oprobst/Bogenampel/specs/005-ota-maintenance-mode/checklists/requirements.md

# Specification Quality Checklist: Receiver OTA Maintenance Mode (button-at-boot)

**Purpose**: Validate specification completeness and quality before proceeding to planning
**Created**: 2026-06-13
**Feature**: [spec.md](../spec.md)

## Content Quality

- [x] No implementation details (languages, frameworks, APIs)
- [x] Focused on user value and business needs
- [x] Written for non-technical stakeholders
- [x] All mandatory sections completed

## Requirement Completeness

- [x] No [NEEDS CLARIFICATION] markers remain
- [x] Requirements are testable and unambiguous
- [x] Success criteria are measurable
- [x] Success criteria are technology-agnostic (no implementation details)
- [x] All acceptance scenarios are defined
- [x] Edge cases are identified
- [x] Scope is clearly bounded
- [x] Dependencies and assumptions identified

## Feature Readiness

- [x] All functional requirements have clear acceptance criteria
- [x] User scenarios cover primary flows
- [x] Feature meets measurable outcomes defined in Success Criteria
- [x] No implementation details leak into specification

## Notes

- Items marked incomplete require spec updates before `/speckit.clarify` or `/speckit.plan`.
- Validation result (2026-06-13): all items pass.
  - "ESP-NOW", "WiFi", "access point", "indicator LED", "button" are treated as user-facing
    product/hardware terms (the receiver's existing physical controls and its radio link), not
    implementation choices — kept because removing them would make the requirements untestable for
    this embedded device.
  - Zero [NEEDS CLARIFICATION] markers: the one open design decision (how OTA and the radio link
    coexist) was resolved with the user before writing the spec (on-demand maintenance mode).
