oprobst/Bogenampel/specs/004-v3-esp32-port/checklists/requirements.md

# Specification Quality Checklist: Bogenampel V3 Hardware Port (ESP32 + e-Paper + ESP-NOW)

**Purpose**: Validate specification completeness and quality before proceeding to planning
**Created**: 2026-06-09
**Feature**: [spec.md](../spec.md)

## Content Quality

- [x] No implementation details (languages, frameworks, APIs) — *see note below*
- [x] Focused on user value and business needs
- [x] Written for non-technical stakeholders
- [x] All mandatory sections completed

## Requirement Completeness

- [x] No [NEEDS CLARIFICATION] markers remain
- [x] Requirements are testable and unambiguous
- [x] Success criteria are measurable
- [x] Success criteria are technology-agnostic (no implementation details) — *see note below*
- [x] All acceptance scenarios are defined
- [x] Edge cases are identified
- [x] Scope is clearly bounded
- [x] Dependencies and assumptions identified

## Feature Readiness

- [x] All functional requirements have clear acceptance criteria
- [x] User scenarios cover primary flows
- [x] Feature meets measurable outcomes defined in Success Criteria
- [x] No implementation details leak into specification — *see note below*

## Notes

- **Deliberate exception on "no implementation details"**: this feature IS a hardware port — the
  target MCUs, the display technology, the radio transport and the pin assignments are the
  requirement, not an implementation choice. They are fixed by the finalized V3 schematics in
  `Schaltung_v3/` and were confirmed by the user (including the decision to rework the brightness
  poti to pin D1 and to keep the V2 two-button menu concept). The spec confines these facts to
  the "Hardware Constraints" section and the platform comparison table; behavioral requirements
  (FR-001…FR-010, FR-012…FR-019 in their observable effects) remain implementation-free. Software
  implementation choices (libraries, ESP-NOW frame format, task structure) are left to the
  planning phase.
- All user decisions captured: two-button navigation with wrap-around (as lived in V2),
  brightness poti reworked from D5 to D1, spec-kit workflow, V2 code untouched.
- Ready for `/speckit.plan` (or `/speckit.clarify` if desired).
