oprobst/Bogenampel/specs/001-archery-timer/checklists/requirements.md

# Specification Quality Checklist: Wireless Archery Range Timer System

**Purpose**: Validate specification completeness and quality before proceeding to planning
**Created**: 2025-12-04
**Feature**: [spec.md](../spec.md)

## Content Quality

- [x] No implementation details (languages, frameworks, APIs)
- [x] Focused on user value and business needs
- [x] Written for non-technical stakeholders
- [x] All mandatory sections completed

## Requirement Completeness

- [x] No [NEEDS CLARIFICATION] markers remain
- [x] Requirements are testable and unambiguous
- [x] Success criteria are measurable
- [x] Success criteria are technology-agnostic (no implementation details)
- [x] All acceptance scenarios are defined
- [x] Edge cases are identified
- [x] Scope is clearly bounded
- [x] Dependencies and assumptions identified

## Feature Readiness

- [x] All functional requirements have clear acceptance criteria
- [x] User scenarios cover primary flows
- [x] Feature meets measurable outcomes defined in Success Criteria
- [x] No implementation details leak into specification

## Validation Results

**Status**: PASSED

All checklist items have been validated and passed. The specification is ready for the next phase.

### Detailed Validation Notes:

1. **Content Quality**: The specification focuses on what the system does (timer control, visual display, audio feedback) and why (range safety, shooter coordination) without mentioning specific technologies like Arduino, nRF24L01+, or WS2812B LEDs.

2. **Requirement Completeness**: All 18 functional requirements are testable and unambiguous. No clarification markers exist. Requirements clearly define system behavior without implementation details.

3. **Success Criteria**: All 10 success criteria are measurable and technology-agnostic:
   - Distance-based metrics (20+ meters)
   - Time-based metrics (±1 second precision, <500ms transitions, <5 second initialization)
   - Reliability metrics (<1% failure rate, 8+ hour operation)
   - Usability metrics (95% success rate without documentation)

4. **User Scenarios**: Five prioritized user stories (P1-P5) cover the complete feature scope from core functionality to maintenance. Each story is independently testable with clear acceptance scenarios using Given-When-Then format.

5. **Edge Cases**: Six edge cases identified covering signal interruption, rapid input, mode changes during operation, initial state, range limits, and power issues.

## Next Steps

The specification is ready for:
- `/speckit.plan` - Proceed directly to implementation planning
- OR `/speckit.clarify` - Optional clarification if additional questions arise

No blocking issues found. Feature is well-specified and ready for planning phase.
