oprobst/Bogenampel/specs/006-shutdown-alarm-gesten/checklists/requirements.md

# Specification Quality Checklist: Entkopplung von Ausschalten und Alarm

**Purpose**: Validate specification completeness and quality before proceeding to planning
**Created**: 2026-08-02
**Feature**: [spec.md](../spec.md)

## Content Quality

- [x] No implementation details (languages, frameworks, APIs)
- [x] Focused on user value and business needs
- [x] Written for non-technical stakeholders
- [x] All mandatory sections completed

## Requirement Completeness

- [x] No [NEEDS CLARIFICATION] markers remain
- [x] Requirements are testable and unambiguous
- [x] Success criteria are measurable
- [x] Success criteria are technology-agnostic (no implementation details)
- [x] All acceptance scenarios are defined
- [x] Edge cases are identified
- [x] Scope is clearly bounded
- [x] Dependencies and assumptions identified

## Feature Readiness

- [x] All functional requirements have clear acceptance criteria
- [x] User scenarios cover primary flows
- [x] Feature meets measurable outcomes defined in Success Criteria
- [x] No implementation details leak into specification

## Notes

- **Alle Punkte erfüllt (Stand 2026-08-02, 2. Durchlauf).**
- Die drei ursprünglich offenen Marker (FR-007, FR-009, FR-010) wurden am
  2026-08-02 vom Auftraggeber entschieden: Dreifachklick mit max. 400 ms
  Klickabstand, beide Tasten gleichwertig, gültig nur in „Schießbetrieb" und
  „Pfeile holen".
- Items marked incomplete require spec updates before `/speckit.clarify` or `/speckit.plan`
