oprobst/Bogenampel/specs/001-benutzer-fuehrung/checklists/requirements.md

# Specification Quality Checklist: Archery Tournament Control System - User Guidance

**Purpose**: Validate specification completeness and quality before proceeding to planning
**Created**: 2025-12-13
**Feature**: [spec.md](../spec.md)

## Content Quality

- [x] No implementation details (languages, frameworks, APIs)
- [x] Focused on user value and business needs
- [x] Written for non-technical stakeholders
- [x] All mandatory sections completed

## Requirement Completeness

- [x] No [NEEDS CLARIFICATION] markers remain
- [x] Requirements are testable and unambiguous
- [x] Success criteria are measurable
- [x] Success criteria are technology-agnostic (no implementation details)
- [x] All acceptance scenarios are defined
- [x] Edge cases are identified
- [x] Scope is clearly bounded
- [x] Dependencies and assumptions identified

## Feature Readiness

- [x] All functional requirements have clear acceptance criteria
- [x] User scenarios cover primary flows
- [x] Feature meets measurable outcomes defined in Success Criteria
- [x] No implementation details leak into specification

## Notes

### Clarifications Resolved (2025-12-13)

All 3 clarification questions have been resolved with user input:

1. **FR-003** - Splash screen duration: **3 seconds** (User selected Option B)
2. **User Story 4, Scenario 3** - Configuration reset behavior: **Retain previous settings** (User selected Option B)
3. **User Story 5, Scenario 3** - Post-alarm display behavior: **Return immediately to previous state without confirmation** (User selected Option C)

### Status

**VALIDATION COMPLETE** - All checklist items pass. Specification is ready for planning phase.

Next step: Run `/speckit.plan` to create the implementation plan.
