oprobst/Bogenampel/specs/003-startup-logo-splash/checklists/requirements.md

# Specification Quality Checklist: Startup-Logo und Splash Screen

**Purpose**: Validate specification completeness and quality before proceeding to planning
**Created**: 2025-12-13
**Feature**: [spec.md](../spec.md)

## Content Quality

- [x] No implementation details (languages, frameworks, APIs)
- [x] Focused on user value and business needs
- [x] Written for non-technical stakeholders
- [x] All mandatory sections completed

## Requirement Completeness

- [x] No [NEEDS CLARIFICATION] markers remain
- [x] Requirements are testable and unambiguous
- [x] Success criteria are measurable
- [x] Success criteria are technology-agnostic (no implementation details)
- [x] All acceptance scenarios are defined
- [x] Edge cases are identified
- [x] Scope is clearly bounded
- [x] Dependencies and assumptions identified

## Feature Readiness

- [x] All functional requirements have clear acceptance criteria
- [x] User scenarios cover primary flows
- [x] Feature meets measurable outcomes defined in Success Criteria
- [x] No implementation details leak into specification

## Validation Summary

**Status**: ✓ PASSED - All quality criteria met
**Validation Date**: 2025-12-13
**Clarifications Resolved**: 1 (button press behavior during splash screen)

### Changes Made During Validation
1. Resolved [NEEDS CLARIFICATION] for button press: Any key press skips to main mode
2. Added FR-007: System must end splash screen on any key press
3. Added acceptance scenario 3 in User Story 2: Key press behavior
4. Added SC-006: Key press response time requirement

## Notes

- All validation items passed
- Specification is ready for `/speckit.clarify` or `/speckit.plan`
