oprobst/Bogenampel/Empfaenger/Config.h

/**
 * @file Config.h
 * @brief Zentrale Konfigurationsdatei für Bogenampel V3 Empfänger (Anzeigeeinheit)
 *
 * Enthält alle Hardware-Pin-Definitionen, Timing-Konstanten und
 * Konfigurationsparameter für den Empfänger.
 *
 * Hardware: Seeed XIAO ESP32C3 (U3) auf der PD-12V-Platine (Rev. 2026-08-03)
 * - WS2811 LED Strip (12V, IC-gesteuert, RGB; 7-Segment + Gruppen), direkt am 12V-Netz
 * - ESP-NOW Funk (integriert, kein externes Modul)
 * - Piezo-Transducer 12V über BC337 (Q3), Lüfter über BSS138 (Q2, Low-Side-PWM)
 * - 3 Potis (Lautstärke, Helligkeit, Lüfter-Drehzahl), Debug-Taster, Status-LED
 *
 * Versorgung (PD-12V-Platine, löst den USB-5V-Aufbau mit Step-up ab):
 * - USB-C → CH224K (U2) verhandelt 12 V → Verpolungsschutz Q1 (AO3401A) + TVS D2
 *   → +12V-Netz: LED-Strip (J7), Piezo (J8), Lüfter (J6)
 * - TSR0.5-2433 (U4): 12 V → 3V3, speist den XIAO über den 3V3-Pin (VUSB unbeschaltet)
 * - L7805 (U1): 12 V → 5 V, versorgt ausschließlich den Pegelwandler U5
 * - U5 74AHCT1G125: Pegelwandler 3,3 → 5 V in der LED-Datenleitung (/OE fest an GND,
 *   nicht invertierend), Ausgang über R14 330 Ω an J7 Pin 2 — ersetzt den früheren
 *   direkten 3,3-V-Anschluss, der Farbkipper (Gelb/Weiß) verursacht hat
 *
 * Verbindliche Pin-Quelle: specs/004-v3-esp32-port/contracts/hardware-pins.md
 * (extrahiert aus Schaltung-Empfaenger/Empfaenger.kicad_sch)
 *
 * ESP32-C3-Strapping-Hinweise (alle im Schaltplan gelöst, Stand 2026-06-10):
 * - GPIO2/D0 (Lautstärke-Poti): Fußpunkt an D4 (POTI_GND) statt GND
 * - GPIO9/D9 (Status-LED): aktiv LOW (3V3 → LED → R6 → Pin)
 * - GPIO8/D8: frei (Lüfter-Tacho bewusst nicht angeschlossen)
 *
 * @date 2026-06-11
 * @version 3.0
 */

#pragma once

#include <Arduino.h>

//=============================================================================
// DEBUG-KONFIGURATION (muss VOR allen anderen Definitionen stehen!)
//=============================================================================

// Debugging aktivieren/deaktivieren
#define DEBUG_ENABLED 0  // 1 = Debug-Ausgaben an, 0 = aus

// Verkürzte Zeiten für Testläufe. Default 0 — eingeschaltet wird das NICHT hier,
// sondern über -DDEBUG_SHORT_TIMES=1 aus der platformio.ini (env:empfaenger-debug
// / empfaenger-debug-ota). So kann ein Testbuild mit 6-Sekunden-Passe nicht
// versehentlich im Feld landen, und Sender und Empfänger werden immer bewusst
// als Paar umgestellt (die Zeittabelle muss auf beiden Geräten gleich sein).
#ifndef DEBUG_SHORT_TIMES
#define DEBUG_SHORT_TIMES 0  // 1 = Verkürzte Zeiten, 0 = Normale Zeiten
#endif

//=============================================================================
// HARDWARE PIN-DEFINITIONEN (XIAO-Nummerierung → GPIO)
//=============================================================================

namespace Pins {

    //-------------------------------------------------------------------------
    // Analoge Eingänge: Potis (alle ADC1 — ADC2 ist mit aktivem Funk unbrauchbar!)
    //-------------------------------------------------------------------------
    constexpr uint8_t VOLUME_POTI     = 2;  // D0/GPIO2 (ADC1_CH2): Lautstärke (J3),
                                            // Schleifer über R3 1k; Fußpunkt an POTI_GND!
    constexpr uint8_t BRIGHTNESS_POTI = 3;  // D1/GPIO3 (ADC1_CH3): Helligkeit (J4),
                                            // über R4 1k (umverdrahtet von D5 — GPIO7 hat keinen ADC)
    constexpr uint8_t FAN_POTI        = 4;  // D2/GPIO4 (ADC1_CH4): Lüfter-Drehzahl (J2),
                                            // Schleifer über R5 1k

    //-------------------------------------------------------------------------
    // Geschalteter Poti-Fußpunkt (Strapping-Fix GPIO2, Befund 2)
    //-------------------------------------------------------------------------
    constexpr uint8_t POTI_GND = 6;  // D4/GPIO6: Fußpunkt des Lautstärke-Potis (J3 Pin 3);
                                     // beim Reset hochohmig → GPIO2 liegt HIGH (Boot ok);
                                     // in setup() FRÜH auf OUTPUT + LOW setzen!

    //-------------------------------------------------------------------------
    // Ausgänge: Signalgeber und Lüfter
    //-------------------------------------------------------------------------
    constexpr uint8_t BUZZER  = 5;   // D3/GPIO5 (LEDC): Piezo 12V-Transducer (J8) über
                                     // R10 2k2 → BC337 (Q3), R12 10k Basis-Pulldown;
                                     // R15 2k2 vom Collector nach +12V (Entlade-Pfad —
                                     // ohne den schwingt der Piezo nicht, nur Brummen).
                                     // ACHTUNG: auf der PD-Platine 2k2 statt der früheren
                                     // 470 Ω (5,4 statt 25 mA) — dafür jetzt 12 V statt 5 V
                                     // am Piezo. Falls zu leise: R15 verkleinern (0,5-W-Typ).
                                     // (GPIO5 ist ADC2, wird aber rein digital genutzt)
    constexpr uint8_t FAN_PWM = 21;  // D6/GPIO21 (LEDC): Gate des BSS138 (Q2, J6 Pin 4);
                                     // Q2 invertiert (Open-Drain auf der PWM-Leitung):
                                     // Gate HIGH = Leitung LOW = langsam! R11 10k =
                                     // Pull-up an 3V3 am Gate → PWM-Leitung beim Boot LOW,
                                     // Lüfter auf Minimaldrehzahl, bis die Firmware
                                     // übernimmt (früh Duty setzen!). R13 10k zieht die
                                     // PWM-Leitung bei sperrendem Q2 sauber auf 3V3.

    //-------------------------------------------------------------------------
    // Ausgänge: LEDs
    //-------------------------------------------------------------------------
    constexpr uint8_t LED_STRIP  = 10;  // D10/GPIO10: WS2811 Data → U5 (74AHCT1G125,
                                        // 3,3→5 V) → R14 330Ω → J7 Pin 2.
                                        // U5 hat KEINEN Eingangs-Pulldown: den Pin in
                                        // setup() SOFORT auf OUTPUT LOW legen, sonst
                                        // floatet der Buffer-Eingang bis FastLED.addLeds()
                                        // und schiebt Müll auf die Datenleitung.
    constexpr uint8_t STATUS_LED = 9;   // D9/GPIO9: Status-LED D3 — AKTIV LOW!
                                        // (3V3 → LED → R9 220Ω → Pin sinkt Strom;
                                        // Strapping-Fix Befund 3, Firmware invertiert)

    //-------------------------------------------------------------------------
    // Eingänge: Taster
    //-------------------------------------------------------------------------
    constexpr uint8_t BTN_DEBUG = 20;  // D7/GPIO20 (J5): Debug-/Testtaster gegen GND,
                                       // INPUT_PULLUP, aktiv LOW

    // Frei/Reserve: D5/GPIO7, D8/GPIO8 (Tacho bewusst nicht angeschlossen)

} // namespace Pins

// Status-LED-Polarität (aktiv LOW, siehe oben)
constexpr uint8_t STATUS_LED_ON  = LOW;
constexpr uint8_t STATUS_LED_OFF = HIGH;

//=============================================================================
// OTA (WiFi-Station + ArduinoOTA, nur im OTA-Wartungsmodus)
//=============================================================================

// wifi_credentials.h (gitignored) definiert WIFI_SSID_OVERRIDE + WIFI_PASS_OVERRIDE.
// Vorlage: wifi_credentials.h.example im Repo-Root.
#if __has_include("wifi_credentials.h")
    #include "wifi_credentials.h"
#endif

namespace OTA {

    constexpr const char* HOSTNAME = "bogenampel-empfaenger";
    // OTA-Passwort (WPA2, min. 8 Zeichen) — ArduinoOTA-Auth (FR-012)
    constexpr const char* PASSWORD = "bogenampel";

    // Heimnetz-WLAN für den OTA-Wartungsmodus — aus wifi_credentials.h. Ohne
    // Zugangsdaten bleibt das Gerät im Wartungsmodus im CONNECTING-Blinken
    // (kein SoftAP-Fallback mehr, FR-009). ESP-NOW läuft im Wartungsmodus nicht.
#ifdef WIFI_SSID_OVERRIDE
    constexpr const char* WIFI_SSID = WIFI_SSID_OVERRIDE;
    constexpr const char* WIFI_PASS = WIFI_PASS_OVERRIDE;
#else
    constexpr const char* WIFI_SSID = "";
    constexpr const char* WIFI_PASS = "";
#endif
    constexpr uint16_t WIFI_TIMEOUT = 10000;  // ms bis zum erneuten WiFi-Connect-Versuch (OTA-Wartungsmodus)

} // namespace OTA

//=============================================================================
// OTA-WARTUNGSMODUS — Status-LED-Signalmuster (D9, aktiv LOW)
// Drei unterscheidbare Muster, alle Zeiten sind Zielwerte (±~50 ms Toleranz):
//   CONNECTING (FR-004a): schnelles kurzes Blitzen      (100 ms an / 500 ms aus)
//   READY      (FR-004b): langsames gleichmäßiges Blinken (500 ms an / 500 ms aus)
//   UPDATING   (FR-004c): leuchtet, alle 500 ms kurz aus  (500 ms an / 100 ms aus)
//=============================================================================

namespace OtaSignal {

    constexpr uint16_t CONNECTING_PERIOD_MS = 600;   // FR-004a
    constexpr uint16_t CONNECTING_ON_MS     = 100;
    constexpr uint16_t READY_PERIOD_MS      = 1000;  // FR-004b
    constexpr uint16_t READY_ON_MS          = 500;
    constexpr uint16_t UPDATING_PERIOD_MS   = 600;   // FR-004c
    constexpr uint16_t UPDATING_ON_MS       = 500;

} // namespace OtaSignal

//=============================================================================
// FUNK (ESP-NOW)
//=============================================================================

namespace Radio {

    // WLAN-Kanal (fest, beide Geräte identisch — espnow-protocol.md)
    constexpr uint8_t CHANNEL = 1;

} // namespace Radio

//=============================================================================
// TIMING-KONSTANTEN
//=============================================================================

namespace Timing {

    // Status-LED-Feedback
    constexpr uint16_t LED_BLINK_DURATION_MS = 100;  // Kurzes Blinken bei Empfang

    // Button Debouncing
    constexpr uint8_t DEBOUNCE_MS = 50;  // 50ms Entprellzeit

    // Buzzer-Feedback
    // Resonanzfrequenz des Transducers (Datenblatt CPS-4013-110PM, rated 3250 Hz):
    // ein Piezo ist GENAU bei seiner Resonanz am lautesten — daneben (vorher 2700 Hz)
    // kaum hörbar. Das ist der Lautstärke-Hebel.
    constexpr uint16_t BUZZER_FREQUENCY_HZ = 3250;

    // Poti-Abtastung (alle Regler live, ≥ 10 Hz — FR-021/FR-022/FR-023)
    constexpr uint16_t POTI_UPDATE_INTERVAL_MS = 100;  // 10 Hz

    // Regler-Vorschau: beim Drehen an Lautstärke-/Helligkeits-Poti läuft eine
    // Vorschau (Ton bzw. "888"-Anzeige), die noch bis zu dieser Zeit nach der
    // letzten Bewegung nachklingt.
    constexpr uint16_t PREVIEW_HOLD_MS = 1000;  // max. 1 s Nachlauf

    // Schießbetrieb — Vorbereitungsphase (Wert wie Sender/Config.h)
    #if DEBUG_SHORT_TIMES
        constexpr uint16_t PREPARATION_TIME_MS = 5000;   // 5 Sekunden (DEBUG)
    #else
        constexpr uint16_t PREPARATION_TIME_MS = 10000;  // 10 Sekunden Vorbereitungsphase
    #endif

    //-------------------------------------------------------------------------
    // Verkürzte Schießzeit für Testläufe (DEBUG_SHORT_TIMES)
    //-------------------------------------------------------------------------
    // 120 s → 6 s, 240 s → 12 s (zusammen mit der 5-s-Vorbereitung läuft eine
    // komplette Passe damit in unter einer Minute durch statt in Minuten).
    //
    // ACHTUNG: Diese Abbildung MUSS in Sender/Config.h und Empfaenger/Config.h
    // identisch bleiben. Der Empfänger zählt die Passe AUTONOM (FR-004) und
    // bekommt per Funk nur CMD_START_120/CMD_START_240 — nie die Dauer selbst.
    // Weichen die beiden Tabellen ab, laufen Ampel und Anzeige auseinander und
    // das Passenende fällt auf zwei verschiedene Sekunden.
    constexpr uint16_t SHOOT_DEBUG_120_SEC = 6;
    constexpr uint16_t SHOOT_DEBUG_240_SEC = 12;

    /**
     * @brief Nominale Schießzeit (120/240 s) → tatsächliche Countdown-Dauer
     * @param nominalSeconds Schießzeit aus dem START-Kommando (120 oder 240)
     * @return im Normalbetrieb der Wert selbst, mit DEBUG_SHORT_TIMES die
     *         verkürzte Testdauer
     */
    constexpr uint16_t shootingSeconds(uint16_t nominalSeconds) {
    #if DEBUG_SHORT_TIMES
        return (nominalSeconds >= 240) ? SHOOT_DEBUG_240_SEC : SHOOT_DEBUG_120_SEC;
    #else
        return nominalSeconds;
    #endif
    }

    // Orange-Phase am Ende der Schießzeit. Im Debug-Modus NICHT 5 s: bei einer
    // 6-s-Passe wäre damit fast der ganze Countdown orange und die Phase als
    // Signal wertlos. 2 s halten den Anteil (33 % / 17 %) nah am Normalbetrieb
    // (30 s von 120 s = 25 %).
    #if DEBUG_SHORT_TIMES
        constexpr uint32_t ORANGE_THRESHOLD_SEC = 2;   // DEBUG
    #else
        constexpr uint32_t ORANGE_THRESHOLD_SEC = 30;  // letzte 30 Sekunden
    #endif

} // namespace Timing

//=============================================================================
// ADC-HILFSFUNKTIONEN
//=============================================================================

namespace Adc {

    // Leichte softwareseitige Rauschunterdrückung: Mehrfachmessung mitteln
    // (Oversampling). Reduziert weißes ADC-Rauschen ~√N, ohne Latenz über die
    // Zeit (Reglerstellung bleibt sofort sichtbar). Default 6 Samples.
    inline uint16_t readAveraged(uint8_t pin, uint8_t samples = 6) {
        uint32_t sum = 0;
        for (uint8_t i = 0; i < samples; i++) {
            sum += analogRead(pin);
        }
        return (uint16_t)(sum / samples);
    }

} // namespace Adc

//=============================================================================
// POTI-ORIENTIERUNG (eine Stelle für alle drei Regler)
//=============================================================================

namespace Poti {

    // ESP32-C3-ADC ist 12-bit.
    constexpr uint16_t ADC_MAX = 4095;

    // Drehrichtung der Regler, HARDWARE-ABHÄNGIG — hier und NUR hier umstellen:
    //   true  = Aufdrehen liefert den HÖHEREN ADC-Wert (PD-12V-Platine,
    //           Rev. 2026-08-03: Schleifer zwischen GND und 3V3 regulär verdrahtet)
    //   false = Poti verpolt verbaut (Vorserien-Aufbau bis 2026-08-05) — dort
    //           lieferte Aufdrehen den KLEINEREN Wert und die Firmware invertierte
    //           an fünf Stellen einzeln.
    // Befund 2026-10-01 auf der fertigen Platine: alle drei Regler liefen falsch
    // herum (aufdrehen = dunkler/leiser/langsamer), weil die Software noch
    // invertierte. Verdrahtung bleibt, Invertierung ist hiermit abgeschaltet.
    constexpr bool ASCENDING = true;

    /**
     * @brief Rohwert → Reglerstellung, unabhängig von der Verdrahtung
     * @param raw gemittelter ADC-Rohwert (0…ADC_MAX)
     * @return 0 = Regler am unteren Anschlag (aus/dunkel/langsam),
     *         ADC_MAX = oberer Anschlag (laut/hell/schnell)
     *
     * Alle Kennlinien und Schwellen im Projekt rechnen mit DIESEM Wert, nie mit
     * dem Rohwert — damit beschreibt ASCENDING die Hardware an genau einer Stelle.
     */
    inline uint16_t level(uint16_t raw) {
        uint16_t clamped = (raw > ADC_MAX) ? ADC_MAX : raw;
        return ASCENDING ? clamped : (uint16_t)(ADC_MAX - clamped);
    }

} // namespace Poti

//=============================================================================
// LAUTSTÄRKE-POTI (D0)
//=============================================================================

namespace Volume {

    // Unterhalb dieser Reglerstellung (Poti::level, NICHT Rohwert) ist der Buzzer
    // KOMPLETT STUMM; darüber quadratische Kennlinie bis volle Lautstärke am
    // oberen Anschlag. Bewusst sehr schmal (2026-10-01): stumm wird es nur noch
    // direkt am unteren Anschlag, der nutzbare Lautstärkeweg beginnt sofort
    // danach. Falls das Stummschalten am Anschlag nicht greift, liegt der
    // ADC-Nullpunkt des Exemplars über diesem Wert → Schwelle wieder anheben.
    constexpr uint16_t OFF_THRESHOLD = 5;  // nur der unterste Anschlag ist stumm

} // namespace Volume

//=============================================================================
// LED STRIP KONFIGURATION (WS2811 12V, IC-gesteuert, RGB)
//=============================================================================

namespace LEDStrip {

    // LED Strip Konfiguration (WS2811 12V — 1 Pixel pro schneidbarem Abschnitt):
    // Strip-Reihenfolge (vom HW-Aufbau bestätigt 2026-06-17):
    // - Gruppe C/D: 12 Pixel (LED 1-12,  Array Index 0-11)
    // - Gruppe A/B: 12 Pixel (LED 13-24, Array Index 12-23)
    // - 3 Digits × 7 Segmente × 2 Pixel = 42 Pixel (Array Index 24-65)
    // Total: 66 Pixel

    // Montage-Orientierung (2026-08-06, fertig verdrahtete Tafel): Der Strip-Anfang
    // (Data-In) sitzt in Leserichtung am FALSCHEN Ende — ohne Korrektur steht die
    // komplette Anzeige exakt um 180° auf dem Kopf. Die Verlegung ist in beiden
    // Bereichen punktsymmetrisch, die Drehung ist deshalb eine reine Indexumkehr
    // je Bereich:
    //   - Ziffernblock  (Index 24-65): 100er ↔ 1er tauschen UND je Ziffer die
    //     Segmente spiegeln (A↔D, B↔E, C↔F; G liegt auf der Drehachse) — das
    //     erledigt die umgekehrte Segment-Iteration in DisplayManager::displayDigit()
    // Die GRUPPENBALKEN sind davon ausdrücklich NICHT betroffen (am Aufbau geprüft
    // 2026-08-06): sie liegen nebeneinander an derselben Seite, nicht einander
    // gegenüber — die Drehung tauscht sie also nicht, ein Software-Tausch würde die
    // Zuordnung erst kaputt machen.
    // Auf false setzen, wenn die Tafel je andersherum aufgebaut/verdrahtet wird.
    constexpr bool ROTATE_180 = true;

    constexpr uint8_t GROUP_CD_LEDS = 12;      // LED 1-12  (Index 0-11)
    constexpr uint8_t GROUP_AB_LEDS = 12;      // LED 13-24 (Index 12-23)
    constexpr uint8_t GROUP_CD_START = 0;                            // C/D zuerst im Strip
    constexpr uint8_t GROUP_AB_START = GROUP_CD_START + GROUP_CD_LEDS;  // A/B direkt dahinter

    constexpr uint8_t LEDS_PER_SEGMENT = 2;    // 2 Pixel pro 7-Segment-Balken (12V-Streifen)
    constexpr uint8_t SEGMENTS_PER_DIGIT = 7;  // 7 Segmente pro Ziffer (B, A, F, G, C, D, E)
    constexpr uint8_t NUM_DIGITS = 3;          // 3 Ziffern (1er, 10er, 100er)
    constexpr uint8_t DIGIT_START = GROUP_CD_LEDS + GROUP_AB_LEDS;  // Ziffern beginnen nach beiden Gruppen

    constexpr uint8_t LEDS_PER_DIGIT = LEDS_PER_SEGMENT * SEGMENTS_PER_DIGIT;  // 14 Pixel pro Ziffer
    constexpr uint8_t TOTAL_LEDS = GROUP_AB_LEDS + GROUP_CD_LEDS + (NUM_DIGITS * LEDS_PER_DIGIT);

    // Start-Indizes für die einzelnen Ziffern (relativ zu DIGIT_START).
    // Die Namen bezeichnen die STELLENWERTIGKEIT, die Reihenfolge im Strip dreht
    // sich mit ROTATE_180 um (die mittlere 10er-Stelle bleibt in beiden Fällen
    // in der Mitte).
    constexpr uint8_t DIGIT_1_START = ROTATE_180 ? DIGIT_START + (2 * LEDS_PER_DIGIT)
                                                 : DIGIT_START;
    constexpr uint8_t DIGIT_10_START = DIGIT_START + LEDS_PER_DIGIT;            // 10er-Stelle (mitte)
    constexpr uint8_t DIGIT_100_START = ROTATE_180 ? DIGIT_START
                                                   : DIGIT_START + (2 * LEDS_PER_DIGIT);

    // Helligkeitsbereich für Poti-Steuerung (FR-022)
    constexpr uint8_t BRIGHTNESS_MIN = 38;      // 15% Helligkeit (weiter herunterdimmbar)

    // Design-Wert 255 (100 %), gültig ab der PD-12V-Platine (Rev. 2026-08-03):
    // Der Strip hängt dort direkt am 12V-PD-Netz, der XIAO an einem eigenen
    // 3V3-Regler (TSR0.5-2433) — der Strip kann die Logikversorgung also nicht mehr
    // in die Knie zwingen. Der frühere Deckel 64 stammt vom USB-5V-Aufbau mit
    // 5V→12V-Step-up (dort brach die 5V-Schiene bei voller Helligkeit ein →
    // ESP-Hang/Reset; stabil war nur ~15 %).
    // Strombedarf bei 255: 66 Pixel × ~20 mA je Farbkanal ≈ 1,3 A einfarbig
    // (Timer/Alarm) bzw. ~4 A bei Weiß → PD-Netzteil mit 12 V / ≥ 2 A verwenden.
    //   → Wert ist der obere Poti-Anschlag; bei Instabilität senken (Richtung
    //     BRIGHTNESS_MIN). ACHTUNG: Am alten USB-Aufbau NICHT mit 255 betreiben!
    constexpr uint8_t BRIGHTNESS_MAX = 255;     // 100 % (PD-12V-Platine)

} // namespace LEDStrip

//=============================================================================
// LÜFTER (PWM über BSS138, Drehzahl vom Poti — FR-023)
//=============================================================================

namespace Fan {

    constexpr uint32_t PWM_FREQUENCY_HZ = 25000;  // ≥ 25 kHz (4-Draht-Lüfter-Spec,
                                                  // außerhalb des Hörbereichs)
    constexpr uint8_t PWM_RESOLUTION_BITS = 8;    // Duty 0-255

    // Unterhalb dieser Reglerstellung (Poti::level, NICHT Rohwert) ist der Lüfter
    // aus (bzw. auf Minimaldrehzahl bei 4-Draht-Lüftern, die per PWM nicht
    // vollständig stoppen). ~2,3 % des Drehwegs am unteren Anschlag.
    constexpr uint16_t OFF_THRESHOLD = 95;  // 4095 − 4000 (Totband wie vorher)

    // Kennlinie Poti → Drehzahl: Gamma < 1 (konkav) verschiebt die Drehzahl-
    // änderung nach "früher" im Drehweg und macht die GEFÜHLTE Änderung gleich-
    // mäßiger (Luftstrom/Lärm ~ Drehzahl^~2,5 → γ≈0,4 linearisiert die Wahrnehmung).
    // Kleiner = mehr Spreizung nach unten; 1,0 = linear. Tunbar.
    constexpr float CURVE_GAMMA = 0.4f;

} // namespace Fan

//=============================================================================
// GRUPPEN-DEFINITIONEN (für 3-4 Schützen Modus)
//=============================================================================

namespace Groups {

    // Gruppen-Typen
    enum class Type : uint8_t {
        GROUP_AB = 0,  // Gruppe A/B
        GROUP_CD = 1   // Gruppe C/D
    };

    // Positions-Marker für 4-State Cycle
    enum class Position : uint8_t {
        POS_1 = 1,  // Position 1 (erste Hälfte der Passe)
        POS_2 = 2   // Position 2 (zweite Hälfte der Passe)
    };

} // namespace Groups

//=============================================================================
// SYSTEMKONSTANTEN
//=============================================================================

namespace System {

    // Versionsinformation
    constexpr const char* VERSION = "Bogenampel Empfaenger V3.0";
    constexpr const char* BUILD_DATE = __DATE__;
    constexpr const char* BUILD_TIME = __TIME__;

    // Serial Baud Rate (für Debugging)
    constexpr uint32_t SERIAL_BAUD = 115200;

    #if DEBUG_ENABLED
        #define DEBUG_PRINT(...)   Serial.print(__VA_ARGS__)
        #define DEBUG_PRINTLN(...) Serial.println(__VA_ARGS__)
        #define DEBUG_PRINTF(...)  Serial.printf(__VA_ARGS__)
    #else
        #define DEBUG_PRINT(...)
        #define DEBUG_PRINTLN(...)
        #define DEBUG_PRINTF(...)
    #endif

} // namespace System

//=============================================================================
// KONFIGURATION VALIDIEREN (zur Compile-Zeit)
//=============================================================================

namespace ConfigValidation {

    // Alle Potis müssen auf ADC1 liegen (GPIO0-4 beim ESP32-C3; GPIO5 = ADC2!)
    static_assert(Pins::VOLUME_POTI <= 4, "VOLUME_POTI must be on ADC1 (radio blocks ADC2)");
    static_assert(Pins::BRIGHTNESS_POTI <= 4, "BRIGHTNESS_POTI must be on ADC1");
    static_assert(Pins::FAN_POTI <= 4, "FAN_POTI must be on ADC1");

    // LED-Gesamtzahl: 66 = 12 (C/D) + 12 (A/B) + 3×7×2 (Ziffern)
    static_assert(LEDStrip::TOTAL_LEDS == 66, "LED strip layout must total 66 pixels (12+12 Gruppen + 42 Ziffern)");

} // namespace ConfigValidation
