oprobst/Bogenampel/Sender/StateMachine.h

/**
 * @file StateMachine.h
 * @brief Haupt-State-Machine für Bogenampel V3 Sender
 *
 * PORT aus V2 (Sender/StateMachine.h): Zustände und Übergänge 1:1
 * (data-model.md §3), umgestellt auf:
 * - e-Paper-Rendering über die Menü-Klassen (EpaperDisplay statt ST7789)
 * - ESP-NOW (RadioManager statt globaler RF24-Funktionen)
 * - NVS (ConfigStore statt EEPROM)
 * - 2-Tasten-Gesten (Feature 006): kurzer Klick = bestätigen/weiter,
 *   3× Klick ≤ 400 ms = Alarm (nur Schießbetrieb und Pfeile holen, FR-010),
 *   beliebiger Taster ≥ 3 s = Power-Off in JEDEM Zustand (FR-002).
 *   Ausschalten und Alarm liegen bewusst auf verschiedenen Bewegungen — vorher
 *   entschied der Betriebszustand darüber, was ein Halten bedeutet.
 *
 * REGRESSION-GUARD (FR-004a): handleShootingPhaseEnd(false) bei Zeitablauf
 * sendet KEIN CMD_STOP — der Empfänger beendet die Passe autonom; das
 * CMD_START für die zweite Gruppe ist nur ein Sync-Signal.
 */

#pragma once

#include "Config.h"
#include "ButtonManager.h"
#include "RadioManager.h"
#include "PowerManager.h"
#include "ConfigStore.h"
#include "EpaperDisplay.h"
#include "ConfigMenu.h"
#include "SplashScreen.h"
#include "PfeileHolenMenu.h"
#include "SchiessBetriebMenu.h"
#include "AlarmScreen.h"
#include "ShutdownScreen.h"
#include "NoticeScreen.h"

/**
 * @brief System-Zustände (Tournament State Machine)
 */
enum class State : uint8_t {
    STATE_SPLASH,          // Splash + Verbindungstest (überspringbar)
    STATE_CONFIG_MENU,     // Konfigurationsmenü (Zeit, Schützenanzahl)
    STATE_PFEILE_HOLEN,    // Turniermodus: Pfeile holen (Pause zwischen Passen)
    STATE_SCHIESS_BETRIEB, // Turniermodus: Schießbetrieb aktiv
    STATE_ALARM            // Alarm: Notfall-Abbruch des Schießbetriebs
};

class StateMachine {
public:
    StateMachine(EpaperDisplay& epd, ButtonManager& btnMgr, RadioManager& radioMgr,
                 PowerManager& powerMgr, ConfigStore& store);

    /**
     * @brief Initialisiert die State Machine (startet im Splash)
     */
    void begin();

    /**
     * @brief Update-Funktion (in loop() aufrufen)
     */
    void update();

    /**
     * @brief Aktuellen Zustand abfragen
     */
    State getCurrentState() const { return currentState; }

    /**
     * @brief Manueller Zustandswechsel
     */
    void setState(State newState);

private:
    EpaperDisplay& epd;
    ButtonManager& buttons;
    RadioManager& radio;
    PowerManager& power;
    ConfigStore& configStore;

    SplashScreen splashScreen;
    ConfigMenu configMenu;
    PfeileHolenMenu pfeileHolenMenu;
    SchiessBetriebMenu schiessBetriebMenu;
    AlarmScreen alarmScreen;
    ShutdownScreen shutdownScreen;
    NoticeScreen noticeScreen;

    State currentState;
    uint32_t stateStartTime;  // Zeitstempel beim Zustandswechsel

    //-------------------------------------------------------------------------
    // Turnierkonfiguration (aus NVS geladen, im Menü geändert)
    //-------------------------------------------------------------------------
    uint16_t shootingTime;   // 120 oder 240 Sekunden
    uint8_t shooterCount;    // 2 (1-2 Schützen) oder 4 (3-4 Schützen)

    //-------------------------------------------------------------------------
    // State Variables: SPLASH
    //-------------------------------------------------------------------------
    bool qualityTestDone;       // Connection Quality Test durchgeführt?
    uint8_t connectionQuality;  // Verbindungsqualität in Prozent (0-100)
    uint32_t qualityDisplayStartTime;
    bool searchStatusShown;     // "Suche Empfaenger" bereits angezeigt

    //-------------------------------------------------------------------------
    // State Variables: PFEILE_HOLEN
    //-------------------------------------------------------------------------
    uint32_t lastConnectionCheck;  // Zeitpunkt der letzten Verbindungsprüfung
    bool lastPingOk;               // Ergebnis des letzten Pings (Statuszeile)

    //-------------------------------------------------------------------------
    // Schützengruppen-Tracking (für 3-4 Schützen Modus)
    //-------------------------------------------------------------------------
    Groups::Type currentGroup;
    Groups::Position currentPosition;

    //-------------------------------------------------------------------------
    // State Variables: SCHIESS_BETRIEB (1-Hz-Flag aus Sender.cpp)
    //-------------------------------------------------------------------------
    bool inPreparationPhase;
    uint32_t preparationSecondsRemaining;
    uint32_t shootingSecondsRemaining;
    uint32_t shootingDurationMs;

    //-------------------------------------------------------------------------
    // State Handlers
    //-------------------------------------------------------------------------
    void handleSplash();
    void handleConfigMenu();
    void handlePfeileHolen();
    void handleSchiessBetrieb();
    void handleAlarm();

    //-------------------------------------------------------------------------
    // State Entry Functions
    //-------------------------------------------------------------------------
    void enterSplash();
    void enterConfigMenu();
    void enterPfeileHolen();
    void enterSchiessBetrieb();
    void enterAlarm();

    /**
     * @brief Behandelt Ende der Schießphase (FR-004a-Regression-Guard!)
     * @param manualStop true = Bediener hat abgebrochen (CMD_STOP senden),
     *        false = Zeitablauf (KEIN Funk — Empfänger endet autonom)
     */
    void handleShootingPhaseEnd(bool manualStop = false);

    //-------------------------------------------------------------------------
    // Hilfsfunktionen
    //-------------------------------------------------------------------------
    bool timeInState(uint32_t milliseconds) const;

    /**
     * @brief Wechselt zur nächsten Schützengruppe im 4er-Zyklus
     * AB_POS1 -> CD_POS2 -> CD_POS1 -> AB_POS2 -> AB_POS1
     */
    void advanceToNextGroup();

    /**
     * @brief Sendet das zur aktuellen Gruppe/Position passende GROUP-Kommando
     * @return Zustellstatus (Aufrufer darf ihn ignorieren, wo er nichts ändert)
     */
    TransmissionResult sendGroupCommand();

    /**
     * @brief Alarm mit App-Level-Retries senden (3 Versuche à 200 ms, V2)
     * @return TX_SUCCESS sobald ein Versuch bestätigt wurde
     */
    TransmissionResult sendAlarmWithRetry();

    /**
     * @brief Sendet CMD_STOP für einen MANUELLEN Abbruch und meldet Fehlschläge
     *
     * Nur für den vom Bediener ausgelösten Abbruch. Der reguläre Zeitablauf
     * sendet weiterhin gar kein CMD_STOP (FR-004a-Guard) — der Empfänger
     * beendet die Passe autonom.
     *
     * Bleibt die Bestätigung aus, blockiert showStopFailedNotice() bis zur
     * Kenntnisnahme: Der Sender wechselt sonst wortlos nach "Pfeile holen",
     * während die Ampel draußen weiterzählt.
     */
    void sendManualStop();

    /**
     * @brief Vollbild-Warnung "Abbruch nicht bestätigt", bis der Bediener quittiert
     *
     * Blockiert bis zu Timing::NOTICE_TIMEOUT_MS oder bis zu einem Tastendruck.
     * Das ist unkritisch: In diesem Zustand läuft am Sender kein Countdown mehr,
     * und der Empfänger arbeitet ohnehin autonom.
     */
    void showStopFailedNotice();

    /**
     * @brief Statuszeile neu zeichnen (Akku/USB/Lader/Funk) + Partial-Refresh
     */
    void refreshStatusLine();

    /**
     * @brief Power-Off-Geste prüfen (beliebiger Taster ≥ 3 s) und abschalten (FR-002)
     *
     * Wird zentral aus update() aufgerufen und gilt damit in JEDEM Zustand —
     * auch im laufenden Schießbetrieb und im Alarm. Das ist unkritisch, weil
     * der Empfänger eine begonnene Passe autonom zu Ende führt (FR-004a).
     */
    void checkPowerOffGesture();

    /**
     * @brief Zustände, in denen die Alarm-Geste ausgewertet wird (FR-010)
     *
     * Nur dort, wo Personen an der Schießlinie stehen können. Im
     * Konfigurationsmenü bliebe zügiges Hochzählen von Werten sonst nicht von
     * einem Dreifachklick unterscheidbar.
     */
    static bool isAlarmCapable(State s);

    /**
     * @brief Abschaltung nach Inaktivität prüfen (Timing::IDLE_POWER_OFF_MS)
     *
     * Nur aus den Wartestates aufrufen: im Schießbetrieb läuft eine Passe ohne
     * Tastendruck weiter, und ein stehender Alarm darf sich nicht selbst
     * stilllegen. Als „Aktivität" zählen Tastendrücke und Zustandswechsel.
     */
    void checkIdleTimeout();

    /**
     * @brief Geordnetes Ausschalten: Screen → hibernate → LOAD aus → LATCH LOW
     * @param reason optionale zweite Zeile auf dem Abschied-Screen
     */
    void doPowerOff(const char* reason = nullptr);
};
