oprobst/Bogenampel/Empfaenger/FanManager.cpp

/**
 * @file FanManager.cpp
 * @brief Implementierung der Lüfter-Steuerung
 */

#include "FanManager.h"
#include "Config.h"

#include <esp_arduino_version.h>
#include <math.h>

namespace {
#if ESP_ARDUINO_VERSION_MAJOR < 3
    // arduino-esp32 2.x: LEDC-Kanal muss manuell vergeben werden
    // (Kanal 0 nutzt der Buzzer in BuzzerManager.cpp)
    constexpr uint8_t LEDC_CHANNEL_FAN = 2;
#endif
}

FanManager::FanManager(uint8_t pwm, uint8_t poti)
    : pwmPin(pwm)
    , potiPin(poti)
    , duty(0)
    , lastUpdateMs(0) {
}

void FanManager::begin() {
#if ESP_ARDUINO_VERSION_MAJOR >= 3
    ledcAttach(pwmPin, Fan::PWM_FREQUENCY_HZ, Fan::PWM_RESOLUTION_BITS);
#else
    ledcSetup(LEDC_CHANNEL_FAN, Fan::PWM_FREQUENCY_HZ, Fan::PWM_RESOLUTION_BITS);
    ledcAttachPin(pwmPin, LEDC_CHANNEL_FAN);
#endif

    // Sofort definierten Duty vom Poti setzen (Befund 6: Gate-Pull-up R11
    // hielt die PWM-Leitung bis hierhin LOW → Lüfter auf Minimaldrehzahl)
    applyPotiValue();
    lastUpdateMs = millis();
}

void FanManager::update() {
    if (millis() - lastUpdateMs < Timing::POTI_UPDATE_INTERVAL_MS) return;
    lastUpdateMs = millis();
    applyPotiValue();
}

void FanManager::applyPotiValue() {
    // Aufdrehen = schneller: Poti::level liefert die Reglerstellung (groß = voll),
    // unterhalb Fan::OFF_THRESHOLD ist der Lüfter aus. Gamma-Kennlinie
    // (Fan::CURVE_GAMMA < 1) spreizt die gefühlte Drehzahländerung über den
    // Drehweg — sonst beschleunigt der Lüfter fast nur im obersten PWM-Bereich.
    // ACHTUNG: Die zweite Invertierung unten (255 − fanDuty) ist KEINE Poti-
    // Korrektur, sondern Hardware: Q2 ist Open-Drain, Gate HIGH zieht die
    // PWM-Leitung LOW = Lüfter langsam. Die muss bleiben.
    uint16_t level = Poti::level(Adc::readAveraged(potiPin));  // gemittelt (Rauschunterdrückung)
    // q = Anteil Richtung volle Drehzahl (0 = Aus-Anschlag, 1 = voll)
    float q = (level <= Fan::OFF_THRESHOLD)
                  ? 0.0f
                  : (float)(level - Fan::OFF_THRESHOLD)
                        / (float)(Poti::ADC_MAX - Fan::OFF_THRESHOLD);
    uint8_t fanDuty = (uint8_t)(powf(q, Fan::CURVE_GAMMA) * 255.0f + 0.5f);  // 255 = voll
    uint8_t newDuty = (uint8_t)(255 - fanDuty);  // Gate-Duty (invertiert: 0 = voll)

    // Kleine Hysterese gegen ADC-Rauschen
    if (newDuty != duty && (newDuty > duty ? newDuty - duty : duty - newDuty) >= 2) {
        duty = newDuty;
#if ESP_ARDUINO_VERSION_MAJOR >= 3
        ledcWrite(pwmPin, duty);
#else
        ledcWrite(LEDC_CHANNEL_FAN, duty);
#endif
    }
}
