oprobst/Bogenampel/Sender/PowerManager.h

/**
 * @file PowerManager.h
 * @brief Soft-Power (Latch), Akku-Messung und Lader-Status (NEU in V3)
 *
 * - Power-Latch GPIO16: HIGH = Gerät bleibt an (allererste Aktion in setup()!),
 *   LOW = Selbstabschaltung (R-13)
 * - Akku: analogReadMilliVolts(GPIO10) × 2,5 (Teiler R4/R8 = 150k/100k),
 *   Median-5-Filter, V2-Schwellen 3,0/3,3/4,2 V (R-11)
 * - Lader MCP73837: STAT1/STAT2/PG Open-Drain → INPUT_PULLUP, Decode nach
 *   Table 5-1 des Datenblatts DS20002071C (R-12)
 * - C_PRG (GPIO18) MUSS hochohmig bleiben: R20 (10k) zieht PROG2 auf Low =
 *   kleiner USB-Ladestrom (80-100 mA, "1 Unit Load").
 *
 *   ⚠ GPIO18 auf OUTPUT HIGH ist KEIN Schnelllade-Opt-in — es schaltet den
 *   Lader ab. Die PROG2-Schwellen sind relativ zu VDD, und VDD = VUSB = 5 V
 *   (VAC ist auf dieser Platine unbeschaltet). Damit gilt VIH >= 0,8*VDD =
 *   4,0 V, waehrend der ESP32 nur 3,3 V liefert. 3,3 V liegt im
 *   Shutdown-Fenster VSD (0,2*VDD .. 0,8*VDD = 1,0 .. 4,0 V) — derselbe
 *   Mechanismus, der den Lader schon beim urspruenglichen 100k-R20 stillgelegt
 *   hat, nur von der anderen Seite. Schnellladen braucht Hardware: R20 als
 *   Pull-up nach VUSB (fest 500 mA) oder Pull-up + N-MOSFET fuer Umschaltung.
 *   Details: specs/004-v3-esp32-port/contracts/hardware-pins.md, Befund 4.
 * - USB-Erkennung: GPIO8 (VBUS-Teiler, aktiv HIGH)
 */

#pragma once

#include <Arduino.h>
#include "Config.h"

/**
 * @brief Lader-Zustand (MCP73837, decodiert aus STAT1/STAT2/PG)
 *
 * Zuordnung strikt nach Table 5-1 „Status Outputs" (DS20002071C, S. 19):
 *
 *   Zustand                     STAT1  STAT2  PG
 *   Shutdown                    Hi-Z   Hi-Z   Hi-Z
 *   Standby                     Hi-Z   Hi-Z   L
 *   Preconditioning / CC / CV   L      Hi-Z   L
 *   Charge Complete – Standby   Hi-Z   L      L
 *   Temperature Fault           Hi-Z   Hi-Z   L
 *   Timer Fault                 Hi-Z   Hi-Z   L
 *   System Test Mode            L      L      L
 */
enum class ChargeState : uint8_t {
    NO_INPUT,   // Shutdown: keine gültige Eingangsspannung (PG Hi-Z)
    CHARGING,   // Preconditioning / Constant Current / Constant Voltage
    COMPLETE,   // Charge Complete – Standby (Akku wirklich voll)
    SUSPENDED,  // Standby / Temperature Fault / Timer Fault — es wird NICHT geladen
    TEST_MODE   // System Test Mode (LDO) — im Normalbetrieb unerwartet
};

class PowerManager {
public:
    PowerManager();

    /**
     * @brief Initialisiert Mess- und Status-Pins (Latch ist bereits gesetzt!)
     *
     * Der LATCH-Pin wird NICHT hier, sondern als allererste Anweisung in
     * setup() gesetzt — sonst schaltet das Gerät beim Loslassen des Einschalt-Tasters ab.
     */
    void begin();

    /**
     * @brief Zyklische Messung (alle 5 s, V2-Intervall) — in loop() aufrufen
     * @return true wenn neue Werte vorliegen (Anzeige aktualisieren)
     */
    bool update();

    uint16_t batteryMv() const { return filteredMv; }
    uint8_t batteryPercent() const;                       // linear 3,0-4,2 V
    bool isLowBattery() const { return filteredMv < Battery::VOLTAGE_LOW_MV; }
    bool isUsbConnected() const { return usbConnected; }
    ChargeState chargeState() const { return charge; }

    /**
     * @brief Latch loslassen — Gerät schaltet sich ab (letzter Schritt!)
     *
     * Reihenfolge davor (Aufrufer): Abschalt-Screen zeichnen →
     * display.hibernate() → LOAD-Rail aus → DANN latchOff().
     */
    void latchOff();

private:
    uint16_t filteredMv;       // Median-gefilterte Akkuspannung
    bool usbConnected;
    ChargeState charge;
    uint32_t lastUpdateMs;

    uint16_t readBatteryMv();  // Einzelmessung × Teilerfaktor
    void readChargerStatus();
};
